sker65/WordclockV3/_Worldclock 3d Print/Komplett druckbar/3d files/wordclock-case_quater1.stl

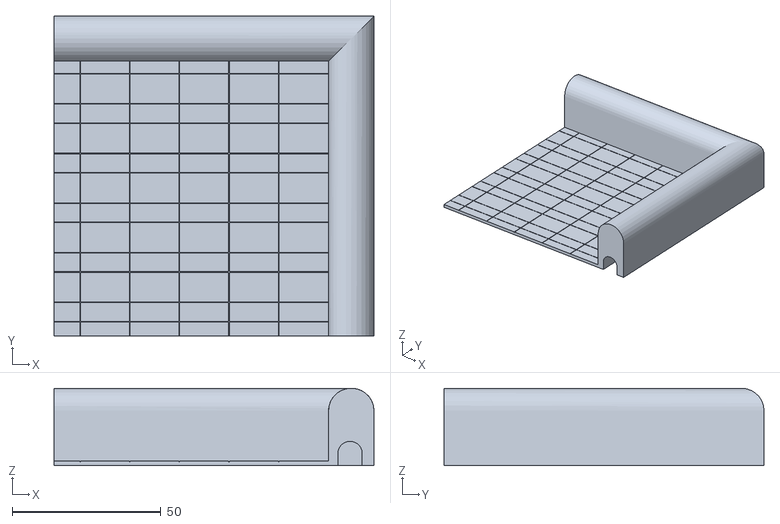
[picture p15: CAD file, 2019-12-11]
_Worldclock 3d Print/Komplett druckbar/3d files/wordclock-case_quater1.stl
107.5 x 107.5 x 26.0
