sker65/WordclockV3/Graphics/Clock_45x45.dxf

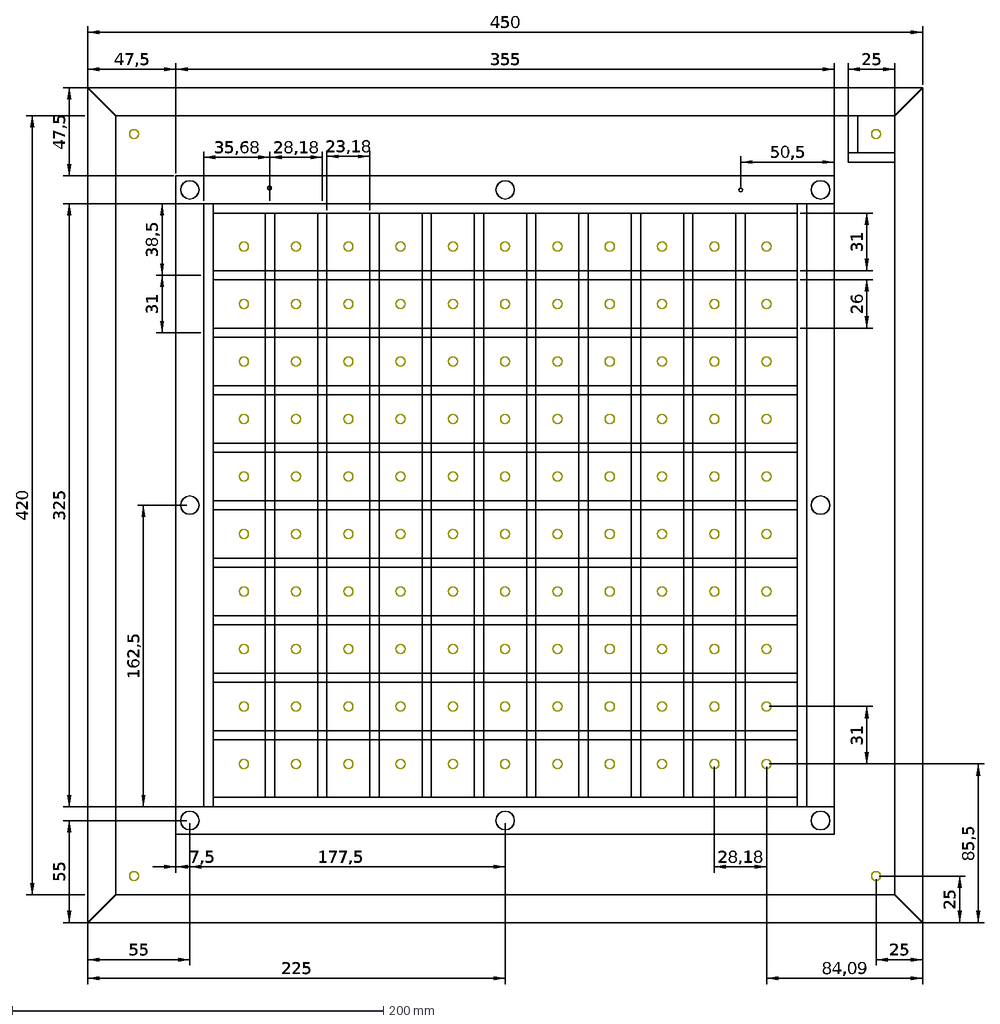
[picture p16: CAD file, 2021-12-20]
Graphics/Clock_45x45.dxf
25
84,09
85,5
55
225
355
450
325
47,5
7,5
177,5
162,5
31
28,18
38,5
35,68
26
420
50,5
23,18
