sker65/WordclockV3/_Worldclock 3d Print/für Ikea Rahmen/Rahmen_Kid4.stl

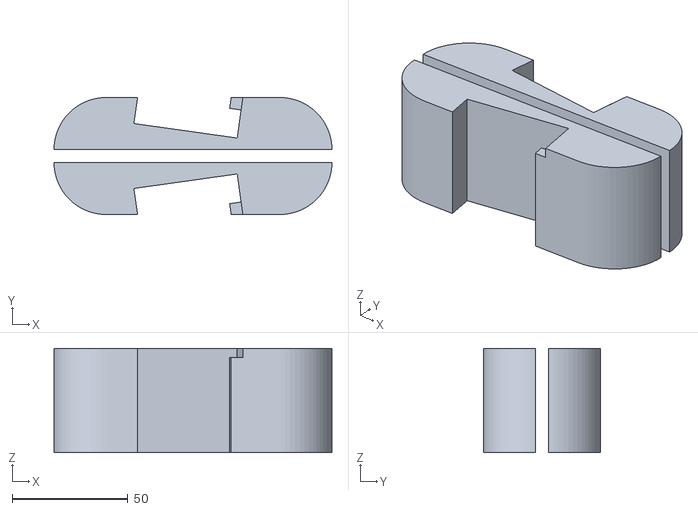
[picture p17: CAD file, 2019-12-10]
_Worldclock 3d Print/für Ikea Rahmen/Rahmen_Kid4.stl
120.0 x 50.5 x 45.0
