sker65/WordclockV3/Graphics/EdelstahlFrontV2.dxf

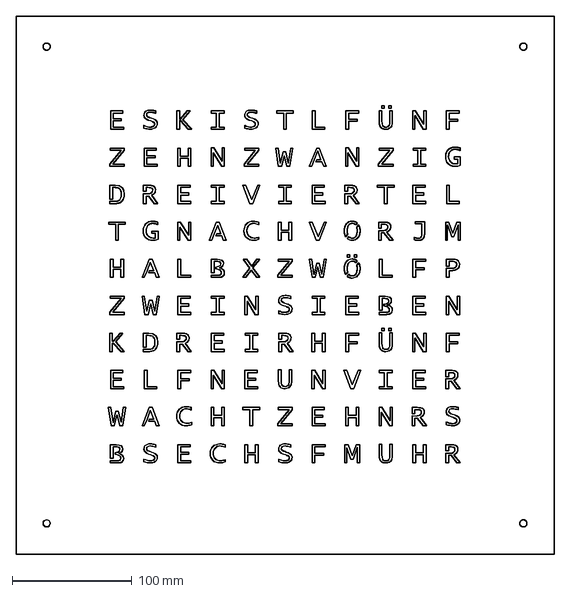
[picture p18: CAD file, 2021-12-20]
Graphics/EdelstahlFrontV2.dxf
449.2 x 449.2 mm
