sker65/WordclockV3/_Worldclock 3d Print/für Ikea Rahmen/Lichtgitter2_2x.stl

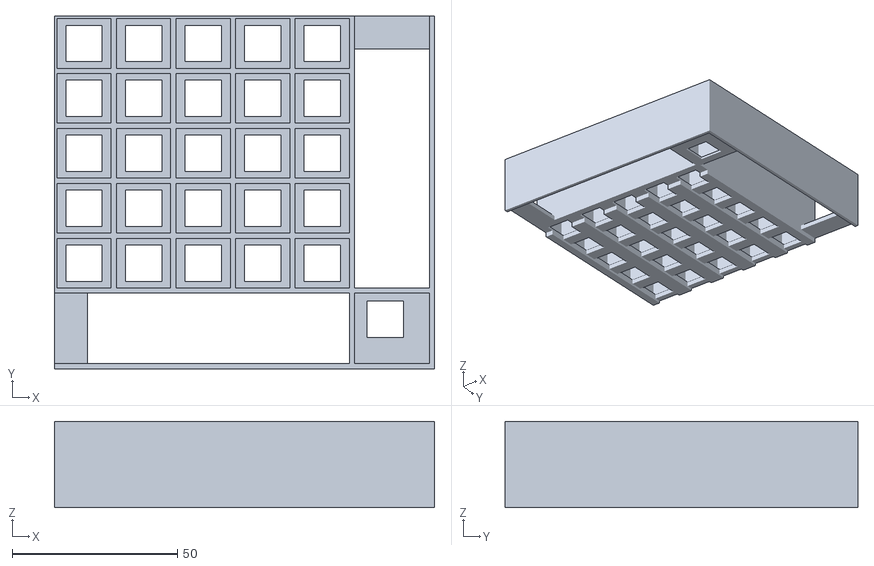
[picture p19: CAD file, 2019-12-10]
_Worldclock 3d Print/für Ikea Rahmen/Lichtgitter2_2x.stl
115.0 x 106.7 x 26.0
