sker65/WordclockV3/_Worldclock 3d Print/Komplett druckbar/3d files/wordclock-bottom-grid_half.stl

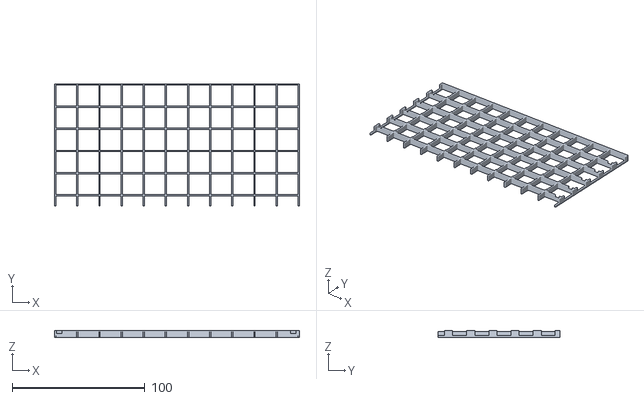
[picture p20: CAD file, 2019-12-10]
_Worldclock 3d Print/Komplett druckbar/3d files/wordclock-bottom-grid_half.stl
184.4 x 92.1 x 5.00
