sker65/WordclockV3/_Worldclock 3d Print/Komplett druckbar/3d files/wordclock_shade.stl

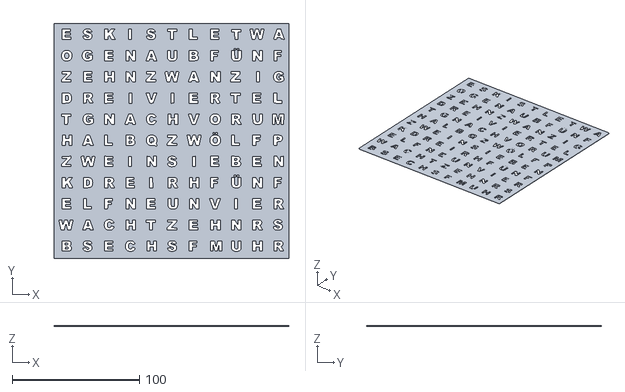
[picture p21: CAD file, 2019-12-10]
_Worldclock 3d Print/Komplett druckbar/3d files/wordclock_shade.stl
184.4 x 184.4 x 1.00
