sker65/WordclockV3/_Worldclock 3d Print/Komplett druckbar/3d files/wordclock-case.stl

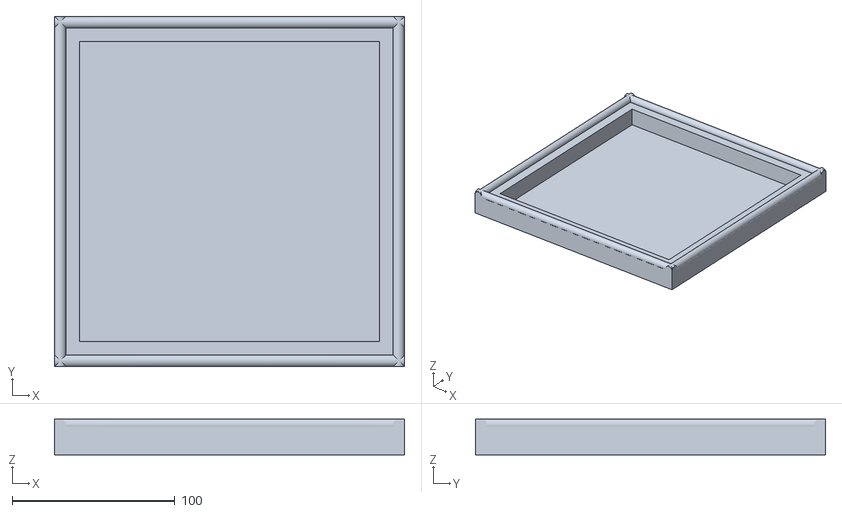
[picture p22: CAD file, 2019-12-10]
_Worldclock 3d Print/Komplett druckbar/3d files/wordclock-case.stl
215.0 x 215.0 x 22.0
