sker65/WordclockV3/_Worldclock 3d Print/Komplett druckbar/3d files/wordclock_shade_plate.stl

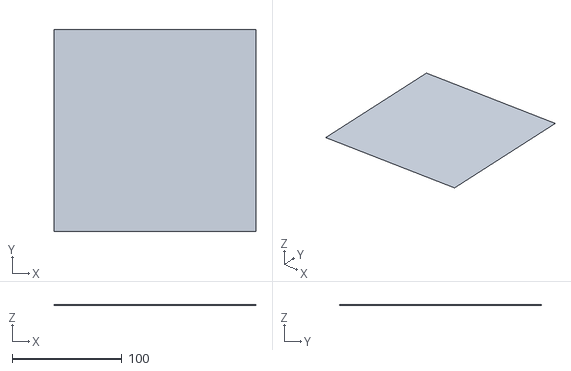
[picture p23: CAD file, 2019-12-10]
_Worldclock 3d Print/Komplett druckbar/3d files/wordclock_shade_plate.stl
184.4 x 184.4 x 0.4
