sker65/WordclockV3/_Worldclock 3d Print/Komplett druckbar/3d files/wordclock-upper-grid_half.stl

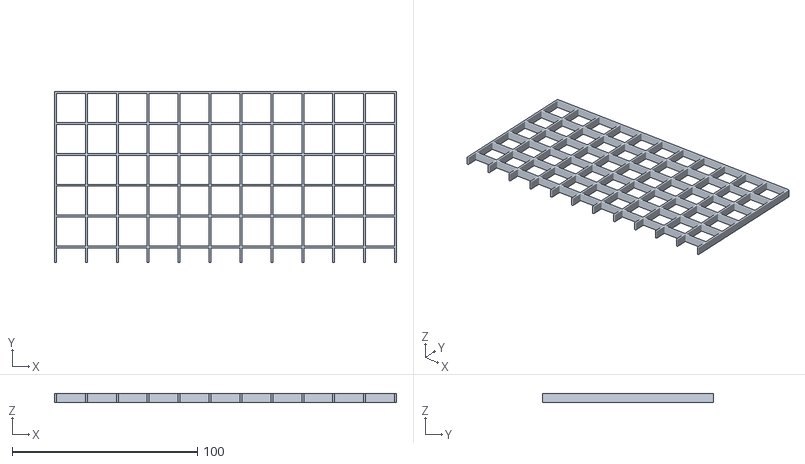
[picture p24: CAD file, 2019-12-10]
_Worldclock 3d Print/Komplett druckbar/3d files/wordclock-upper-grid_half.stl
184.4 x 92.2 x 5.00
