sker65/WordclockV3/_Worldclock 3d Print/Komplett druckbar/3d files/wordclock-case_half.stl

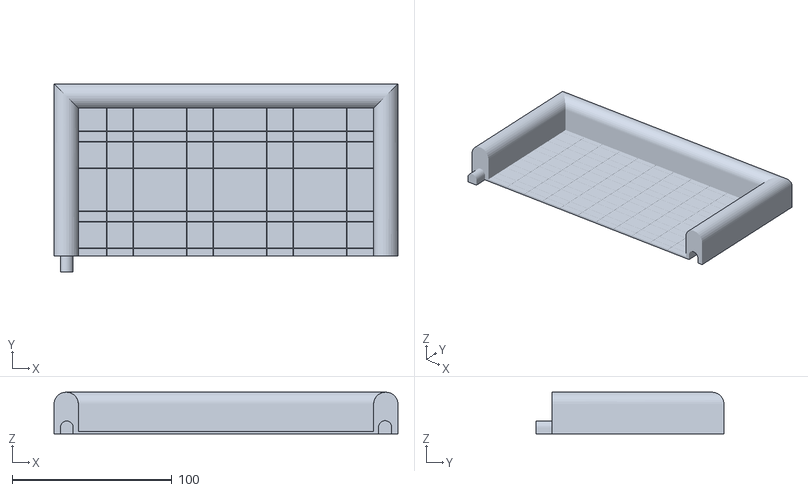
[picture p25: CAD file, 2019-12-10]
_Worldclock 3d Print/Komplett druckbar/3d files/wordclock-case_half.stl
215.0 x 117.5 x 26.0
