sker65/WordclockV3/_Worldclock 3d Print/druckbar 2/images/image6.jpeg

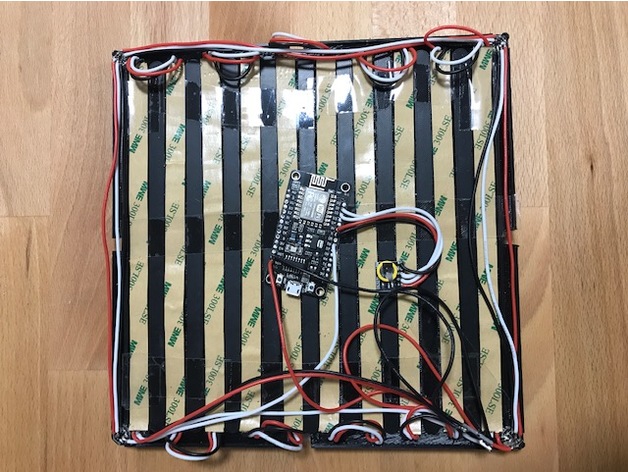
_Worldclock 3d Print/druckbar 2/images/image6.jpeg
