sker65/WordclockV3/_Worldclock 3d Print/druckbar 2/images/Wordclock_Backplate.png

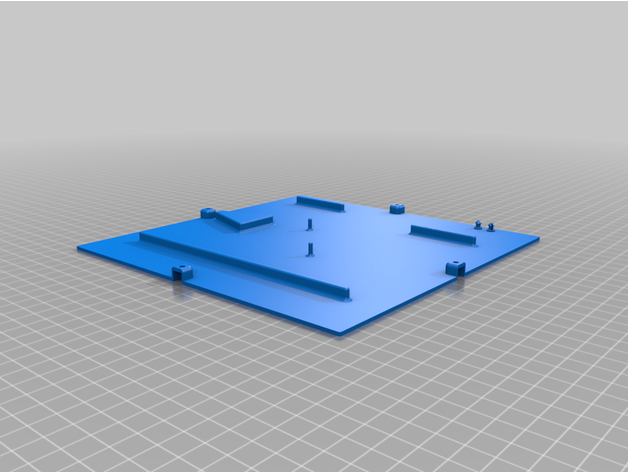
_Worldclock 3d Print/druckbar 2/images/Wordclock_Backplate.png
