sker65/WordclockV3/_Worldclock 3d Print/für Ikea Rahmen/Uhr_Neu/Folie.jpg

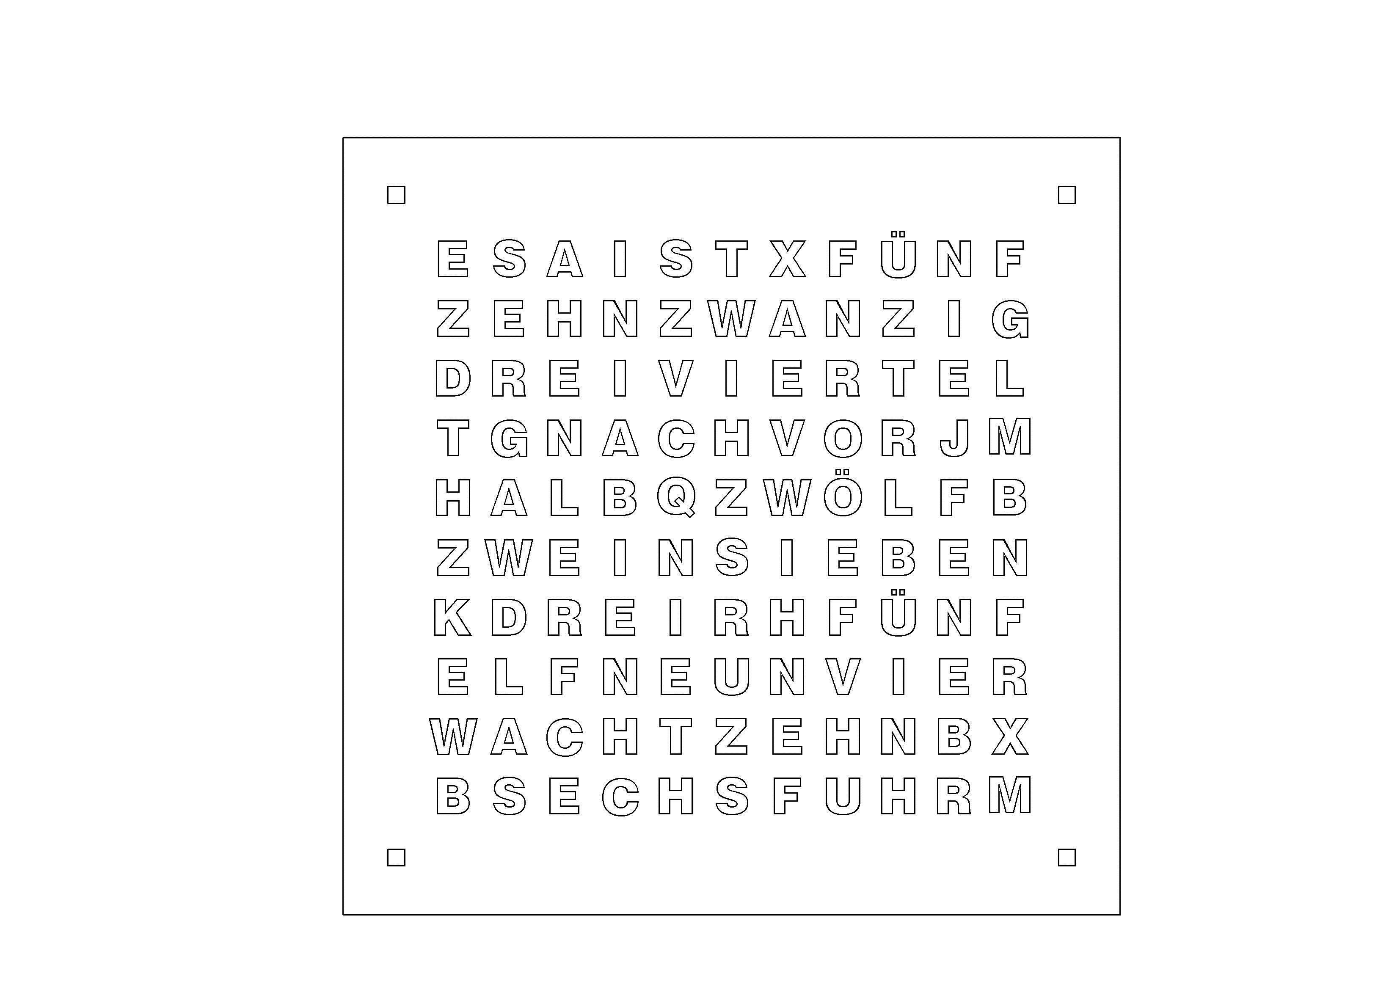
_Worldclock 3d Print/für Ikea Rahmen/Uhr_Neu/Folie.jpg
