sker65/WordclockV3/_Worldclock 3d Print/Komplett druckbar/images/4bb9148eca88c553b5c8efdd03054ffa_preview_featured.JPG

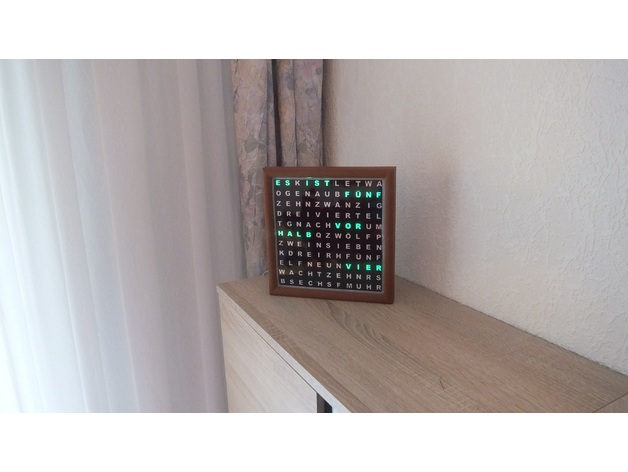
_Worldclock 3d Print/Komplett druckbar/images/4bb9148eca88c553b5c8efdd03054ffa_preview_featured.JPG
