sker65/WordclockV3/_Worldclock 3d Print/Komplett druckbar/images/07bff48b2798516738badc5302d3c22c_preview_featured.jpg

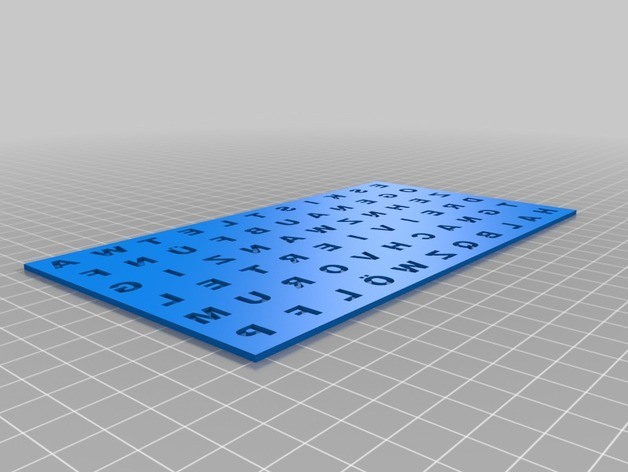
_Worldclock 3d Print/Komplett druckbar/images/07bff48b2798516738badc5302d3c22c_preview_featured.jpg
