sker65/WordclockV3/_Worldclock 3d Print/Komplett druckbar/images/11a6e63ddd8fb1385e88a43530def74b_preview_featured.jpg

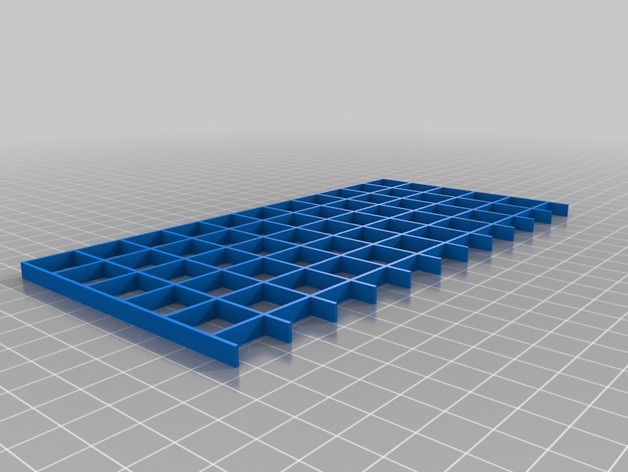
_Worldclock 3d Print/Komplett druckbar/images/11a6e63ddd8fb1385e88a43530def74b_preview_featured.jpg
