sker65/WordclockV3/_Worldclock 3d Print/Komplett druckbar/images/8287f779f04c805deb58c081a0fa2170_preview_featured.jpg

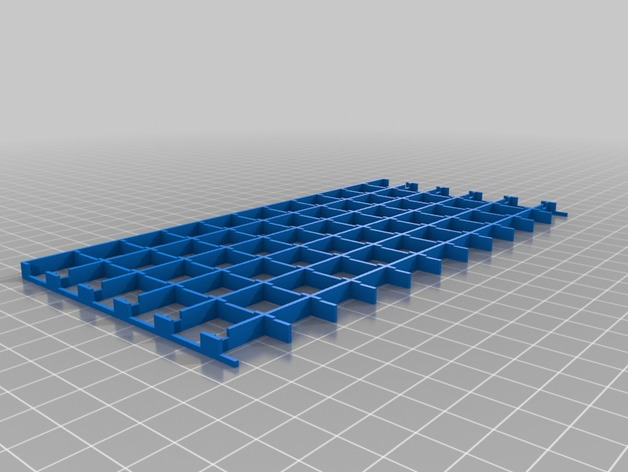
_Worldclock 3d Print/Komplett druckbar/images/8287f779f04c805deb58c081a0fa2170_preview_featured.jpg
