sker65/WordclockV3/_Worldclock 3d Print/Komplett druckbar/images/ab4bcd1fc5b5c4c5ae0cb85b849bbd68_preview_featured.jpg

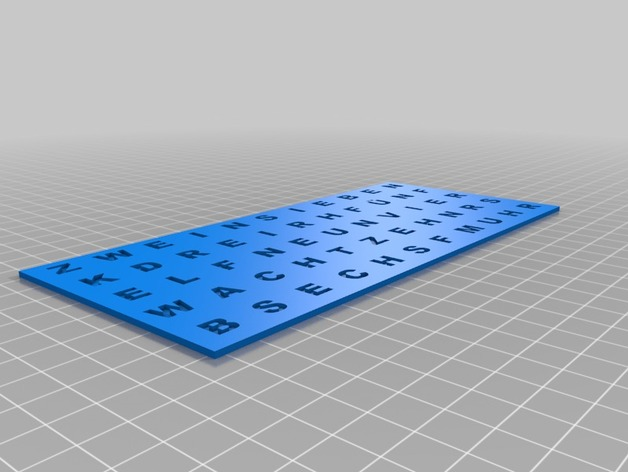
_Worldclock 3d Print/Komplett druckbar/images/ab4bcd1fc5b5c4c5ae0cb85b849bbd68_preview_featured.jpg
