sker65/WordclockV3/_Worldclock 3d Print/Komplett druckbar/images/ab1242061ede618438a3f7739986505e_preview_featured.jpg

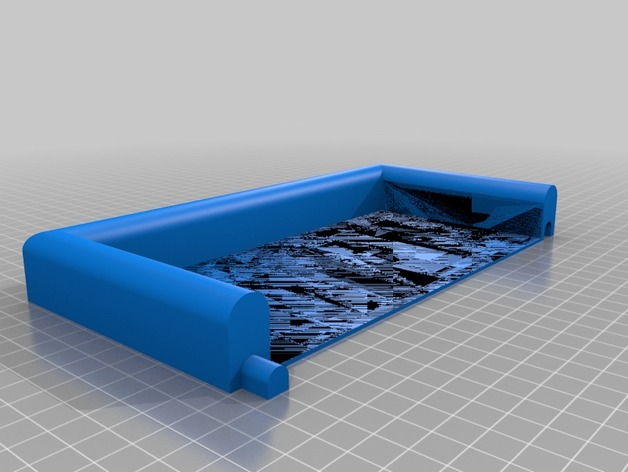
_Worldclock 3d Print/Komplett druckbar/images/ab1242061ede618438a3f7739986505e_preview_featured.jpg
