sker65/WordclockV3/_Worldclock 3d Print/Komplett druckbar/images/c5b8c46510b9335382b88bf6c32e3454_preview_featured.jpg

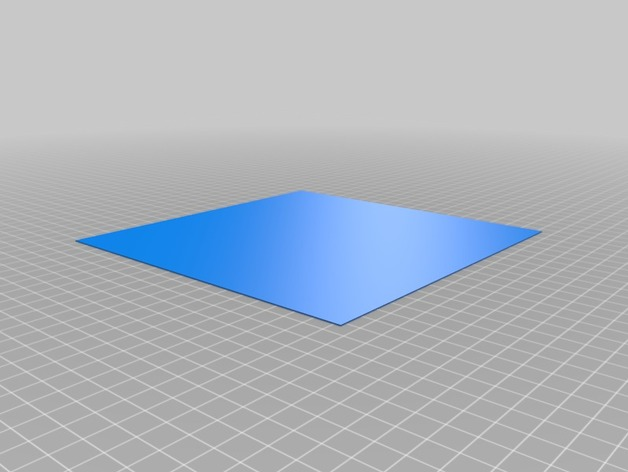
_Worldclock 3d Print/Komplett druckbar/images/c5b8c46510b9335382b88bf6c32e3454_preview_featured.jpg
