sker65/WordclockV3/_Worldclock 3d Print/Komplett druckbar/images/cd97b52f5bf57df827bd3810bf3d21ef_preview_featured.JPG

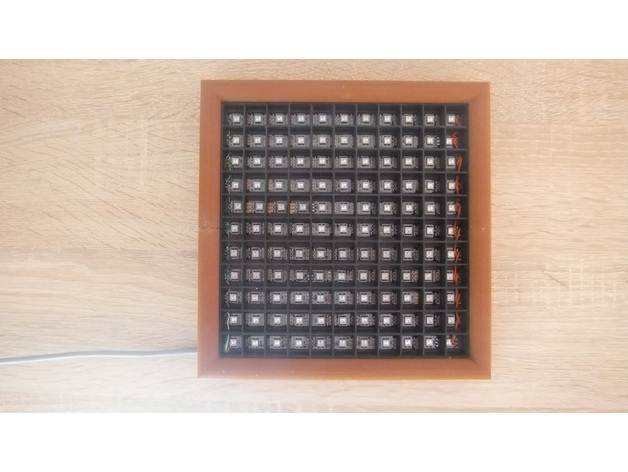
_Worldclock 3d Print/Komplett druckbar/images/cd97b52f5bf57df827bd3810bf3d21ef_preview_featured.JPG
