sker65/WordclockV3/_Worldclock 3d Print/Komplett druckbar/images/e88713d8dcbdc250f0a9445fbaead185_preview_featured.JPG

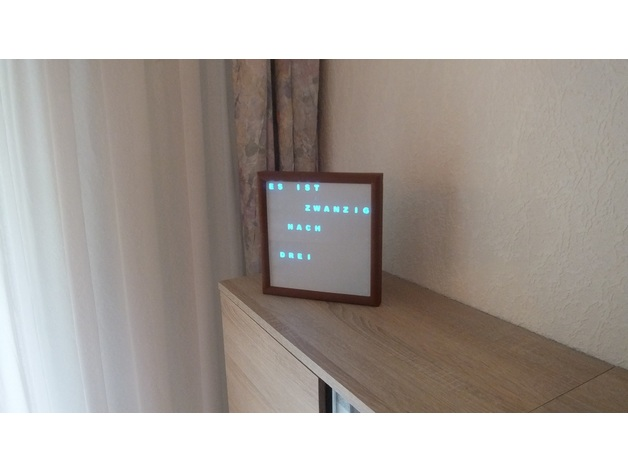
_Worldclock 3d Print/Komplett druckbar/images/e88713d8dcbdc250f0a9445fbaead185_preview_featured.JPG
