sker65/WordclockV3/letters.h

#pragma once

// taken from https://github.com/ch570512/Qlockwork
// clang-format off
const char lettersBig[][7] =
{
	{ 0x00, 0x00, 0x00, 0x00, 0x00, 0x00, 0x00 }, // ASCII-Code 0x20 =>   (32)
	{ 0x04, 0x04, 0x04, 0x04, 0x04, 0x00, 0x04 }, // ASCII-Code 0x21 => ! (33)
	{ 0x14, 0x14, 0x14, 0x00, 0x00, 0x00, 0x00 }, // ASCII-Code 0x22 => " (34)
	{ 0x0a, 0x0a, 0x1f, 0x0a, 0x1f, 0x0a, 0x0a }, // ASCII-Code 0x23 => # (35)
	{ 0x04, 0x0f, 0x14, 0x0e, 0x05, 0x1e, 0x04 }, // ASCII-Code 0x24 => $ (36)
	{ 0x18, 0x19, 0x02, 0x04, 0x08, 0x13, 0x03 }, // ASCII-Code 0x25 => % (37)
	{ 0x0c, 0x12, 0x14, 0x08, 0x15, 0x12, 0x0d }, // ASCII-Code 0x26 => & (38)
	{ 0x18, 0x08, 0x10, 0x00, 0x00, 0x00, 0x00 }, // ASCII-Code 0x27 => ' (39)
	{ 0x02, 0x04, 0x08, 0x08, 0x08, 0x04, 0x02 }, // ASCII-Code 0x28 => ( (40)
	{ 0x10, 0x08, 0x04, 0x04, 0x04, 0x08, 0x10 }, // ASCII-Code 0x29 => ) (41)
	{ 0x00, 0x04, 0x15, 0x0e, 0x15, 0x04, 0x00 }, // ASCII-Code 0x2A => * (42)
	{ 0x00, 0x04, 0x04, 0x1f, 0x04, 0x04, 0x00 }, // ASCII-Code 0x2B => + (43)
	{ 0x00, 0x00, 0x00, 0x00, 0x18, 0x08, 0x10 }, // ASCII-Code 0x2C => , (44)
	{ 0x00, 0x00, 0x00, 0x1f, 0x00, 0x00, 0x00 }, // ASCII-Code 0x2D => - (45)
	{ 0x00, 0x00, 0x00, 0x00, 0x00, 0x00, 0x04 }, // ASCII-Code 0x2E => . (46)
	{ 0x00, 0x01, 0x02, 0x04, 0x08, 0x10, 0x00 }, // ASCII-Code 0x2F => / (47)

	{ 0x0e, 0x11, 0x13, 0x15, 0x19, 0x11, 0x0e }, // ASCII-Code 0x30 => 0 (48)

	{ 0x04, 0x0c, 0x04, 0x04, 0x04, 0x04, 0x0e }, // ASCII-Code 0x31 => 1 (49)
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
	{ 0x04, 0x04, 0x04, 0x04, 0x04, 0x04, 0x04 }, // ASCII-Code 0x7C => | (124) 
	{ 0x10, 0x08, 0x08, 0x04, 0x08, 0x08, 0x10 }, // ASCII-Code 0x7D => } (125) 
	{ 0x00, 0x00, 0x00, 0x19, 0x26, 0x00, 0x00 }  // ASCII-Code 0x7E => ~ (126) 
};
// clang-format on
