sker65/WordclockV3/config.h

// ESP8266 Wordclock
// Copyright (C) 2016 Thoralt Franz, https://github.com/thoralt
//
//  See config.cpp for description.
//
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
// You should have received a copy of the GNU General Public License
// along with this program.  If not, see <http://www.gnu.org/licenses/>.
#ifndef _CONFIG_H_
#define _CONFIG_H_

#include <IPAddress.h>

#define NUM_PIXELS 114
#define HOURGLASS_ANIMATION_FRAMES 8

// structure to encapsulate a color value with red, green and blue values
typedef struct _palette_entry {
	uint8_t r, g, b;
} palette_entry;

// structure with configuration data to be stored in EEPROM
typedef struct _config_struct {
	uint32_t magic;
	palette_entry bg;
	palette_entry fg;
	palette_entry s;
	uint8_t ntpserver[4];
	bool heartbeat;
	uint32_t mode;
	uint32_t timeZone;
	bool showItIs;
	uint8_t minuteType;
	bool fgRainbow;
	uint8_t rainbowSpeed;
	bool autoOnOff;
	uint8_t autoOnHour;
	uint8_t autoOnMin;
	uint8_t autoOffHour;
	uint8_t autoOffMin;
	uint8_t tmpl;
	uint8_t fillMode;
} config_struct;

#define EEPROM_SIZE 512

enum class DisplayMode {
	plain,
	fade,
	flyingLettersVerticalUp,
	flyingLettersVerticalDown,
	explode,
	random,
	matrix,
	heart,
	fire,
	plasma,
	stars,
	snake,
	moon,
	red,
	green,
	blue,
	yellowHourglass,
	greenHourglass,
	update,
	updateComplete,
	updateError,
	wifiManager,
	invalid
};
#define MAX_DISPLAY_MODE_TO_SET 21

class ConfigClass {
public:
	// public methods
	ConfigClass();
	virtual ~ConfigClass();
	void begin();
	void save();
	void saveDelayed();
	void load();
	void reset();

	// public configuration variables
	palette_entry fg;
	palette_entry bg;
	palette_entry s;
	IPAddress ntpserver = IPAddress( 0, 0, 0, 0 );
	bool heartbeat = true;
	bool showItIs = true;
	bool fgRainbow = false;
	uint8_t minuteType = 1;
	uint8_t rainbowSpeed = 0;
	bool autoOnOff = false;
	uint8_t autoOnHour;
	uint8_t autoOnMin;
	uint8_t autoOffHour;
	uint8_t autoOffMin;
	uint8_t tmpl;
	uint8_t fillMode;

	bool debugMode = false;
	int delayedWriteTimer = 0;
	bool delayedWriteFlag = false;

	DisplayMode defaultMode = DisplayMode::flyingLettersVerticalUp;

	int updateProgress = 0;
	int hourglassState = 0;
	int timeZone = 0;

private:
	// copy of EEPROM content
	config_struct* config = (config_struct*)eeprom_data;
	uint8_t eeprom_data[EEPROM_SIZE];
};

extern ConfigClass Config;

#endif /* CONFIG_H_ */
