sker65/WordclockV3/brightness.cpp

// ESP8266 Wordclock
// Copyright (C) 2016 Thoralt Franz, https://github.com/thoralt
//
//  This class reads the analog input with an attached light dependent resistor
//  (pullup to VCC, LDR to ground), filters the resulting ADC values with an
//  moving average filter and calculates a brightness value using an interpolation
//  on a curve defined by several points.
//
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
// You should have received a copy of the GNU General Public License
// along with this program.  If not, see <http://www.gnu.org/licenses/>.
#include "brightness.h"
#include <Arduino.h>

//---------------------------------------------------------------------------------------
// global instance
//---------------------------------------------------------------------------------------
BrightnessClass Brightness = BrightnessClass();

//---------------------------------------------------------------------------------------
// BrightnessClass
//
// Constructor, initializes filter with current ADC value
//
// -> --
// <- --
//---------------------------------------------------------------------------------------
BrightnessClass::BrightnessClass() { this->avg = analogRead( A0 ); }

//---------------------------------------------------------------------------------------
// filter
//
// Exponential moving average filter using integer arithmetics. Implements the
// following behaviour:
//
//   output = (1-coeff)*last_output + coeff*input
//
// FILTER_COEFFICIENT is defined as fixed point number with 16.16 bits resolution.
//
// -> input: filter input [0...65535]
// <- --
//---------------------------------------------------------------------------------------
uint32_t BrightnessClass::filter( uint16_t input ) {
	uint32_t tmp = ( 65536 - FILTER_COEFFICIENT ) * this->avg + FILTER_COEFFICIENT * (uint32_t)input;
	return ( tmp + 32768 ) >> 16;
}

//---------------------------------------------------------------------------------------
// getBrightnessForADCValue
//
// Calculates a brightness value for a given ADC value using a table and interpolation.
//
// -> adcValue: input value [0...1023]
// <- brightness [0...256]
//---------------------------------------------------------------------------------------
uint32_t BrightnessClass::getBrightnessForADCValue( uint32_t adcValue ) {
	// clang-format off
//mit LDR:
//	float lightTable[] = {
//		0, 15,
//		59, 35,
//		67, 50,
//		155, 100,
//		750, 200,
//		1023, 255,
//		-1, -1
//	};
//ohne LDR:
	float lightTable[] = {
		0, 255,
		1023, 255,
		-1, -1
	};
	// clang-format on
	if( this->brightnessOverride < 256 ) {
		return this->brightnessOverride;
	}

	int i = 0;
	float result;
	float value = adcValue;
	while( lightTable[i] != -1 ) {
		if( adcValue >= lightTable[i] && adcValue < lightTable[i + 2] ) {
			float x1 = lightTable[i + 0];
			float y1 = lightTable[i + 1];
			float x2 = lightTable[i + 2];
			float y2 = lightTable[i + 3];
			result = y1 + ( value - x1 ) * ( y2 - y1 ) / ( x2 - x1 );
			return (int)result;
		}
		i += 2;
	}

	return 0;
}

//---------------------------------------------------------------------------------------
// value
//
// Triggers a new sample to be read from light sensor, returns value from average filter
//
// -> --
// <- low pass filtered brightness value
//---------------------------------------------------------------------------------------
uint32_t BrightnessClass::value() {
	// read next ADC value and apply filter
	this->avg = this->filter( analogRead( A0 ) );

	// calculate brightness value for filtered ADC value
	return this->getBrightnessForADCValue( this->avg );
}
