sker65/WordclockV3/matrixobject.cpp

// ESP8266 Wordclock
// Copyright (C) 2016 Thoralt Franz, https://github.com/thoralt
//
//  This class represents one "Matrix Pixel" for the matrix screen saver.
//
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
#include "matrixobject.h"
#include "ledfunctions.h"

//---------------------------------------------------------------------------------------
// initializes the static gradient palette
//---------------------------------------------------------------------------------------
// clang-format off
const std::vector<palette_entry> MatrixObject::MatrixGradient = {
	{ 255, 255, 255 },
	{ 128, 255, 128 },
	{ 64, 255, 64 },
	{ 0, 255, 0 },
	{ 0, 128, 0 },
	{ 0, 64, 0 },
	{ 0, 32, 0 },
	{ 0, 16, 0 },
	{ 0, 8, 0 },
	{ 0, 2, 0 },
	{ 0, 1, 0 },
	{ 0, 0, 0 } };
// clang-format on
//---------------------------------------------------------------------------------------
// MatrixObject
//
// Constructor. Initializes coordinates and speed with random values.
//
// -> --
// <- --
//---------------------------------------------------------------------------------------
MatrixObject::MatrixObject() { this->randomize(); }

//---------------------------------------------------------------------------------------
// move
//
// Moves the matrix object using prescaler. Assigns new random coordinates if object
// leaves screen.
//
// -> --
// <- --
//---------------------------------------------------------------------------------------
void MatrixObject::move() {
	this->prescaler += this->speed;
	if( this->prescaler > 30000 ) {
		this->prescaler -= 30000;
		this->y++;
		int limit = LEDMatrix::height + MatrixObject::MatrixGradient.size();
		if( this->y > limit )
			this->randomize();
	}
}

//---------------------------------------------------------------------------------------
// randomize
//
// Assigns new random coordinates, initializes speed and prescaler counter.
//
// -> --
// <- --
//---------------------------------------------------------------------------------------
void MatrixObject::randomize() {
	this->x = random( LEDMatrix::width ); //   0 ... width
	this->y = random( 25 ) - 25;          // -25 ... -1
	this->speed = MatrixObject::MinMatrixSpeed + random( MatrixObject::MaxMatrixSpeed - MatrixObject::MinMatrixSpeed );
	this->prescaler = 0;
}

//---------------------------------------------------------------------------------------
// render
//
// Moves and renders the matrix object to an RGB buffer. Uses the MatrixGradient palette
// to draw the matrix stream object from bottom to top.
//
// -> buf: Pointer to render target (linear RGB buffer)
// <- --
//---------------------------------------------------------------------------------------
void MatrixObject::render( uint8_t* buf ) {
	this->move();

	// check boundaries
	if( this->x < 0 || this->x >= LEDMatrix::width )
		return;

	int currentY = this->y;
	int ofs;

	for( palette_entry p : MatrixObject::MatrixGradient ) {
		// only render if inside screen rectangle
		if( currentY >= 0 && currentY < LEDMatrix::height ) {
			ofs = LEDMatrix::getOffset( this->x, currentY );
			buf[ofs + 0] = p.r;
			buf[ofs + 1] = p.g;
			buf[ofs + 2] = p.b;
		}
		currentY--;
	}
}
